nealpalmer/UsbJoy/software/UsbJoy_firmware/usbjoystick_d12a4r3/main.cpp

#include <Arduino.h>
#include "Joystick.h"

/*
Joystick_ joystick;

uint8_t data[4];
int previousStates[6];

void setup() {
    Serial.begin(9600);
    pinMode(LED_BUILTIN, OUTPUT);
    for (int i = 2; i < 8; ++i) {
        pinMode(i, INPUT_PULLUP);
        previousStates[i - 2] = 0;
    }

    joystick.begin();
    DynamicHID().prepareOutput(data, sizeof(data));
}

void loop() {
    int availableData = DynamicHID().available();
    if (availableData > 0) {
        uint8_t firstByte = DynamicHID().read();
        for (int i = 0; i < availableData - 1; i++) {
            DynamicHID().read();
        }

        if (bitRead(firstByte, 0)) {
            digitalWrite(LED_BUILTIN, 1);
        } else {
            digitalWrite(LED_BUILTIN, 0);
        }
    }

    for (int i = 2; i < 8; ++i) {
        int readValue = digitalRead(i);
        if (readValue != previousStates[i - 2]) {
            previousStates[i - 2] = readValue;
            joystick.setButton(i - 2, readValue);
        }
    }
}
*/
